meepodeep/meepolab/Key testing/Body140.3mf

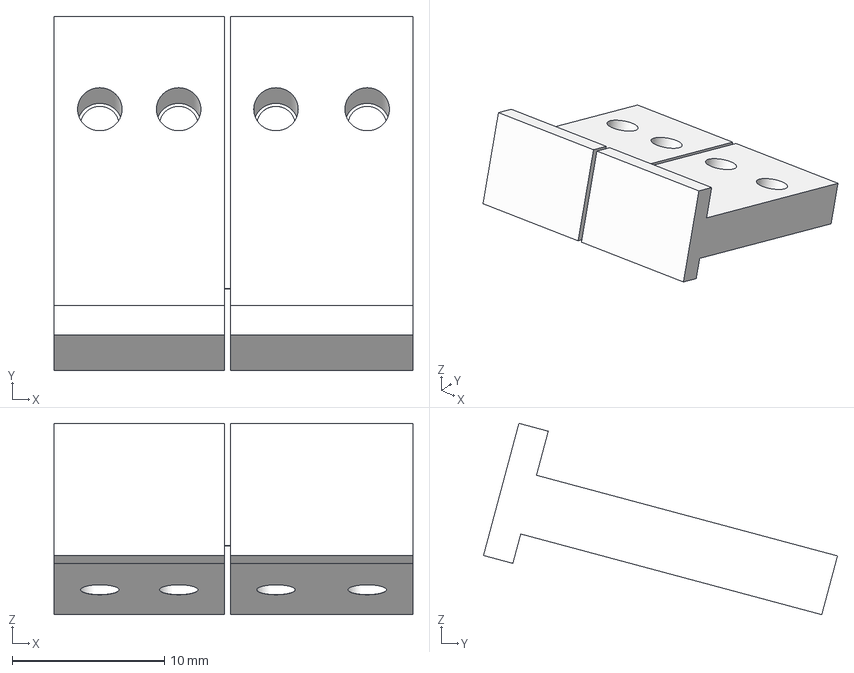
[picture p14: CAD file, 2026-06-28]
Key testing/Body140.3mf
23.6 x 23.3 x 12.6 mm
