meepodeep/meepolab/Key testing/BackPlate (2).3mf

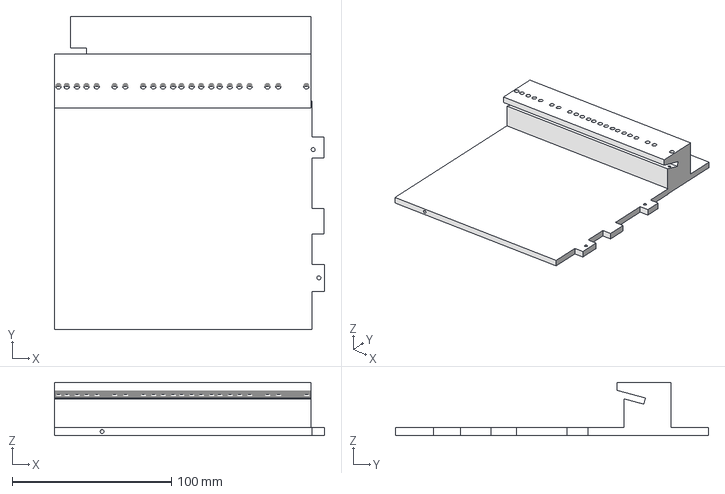
[picture p15: CAD file, 2026-06-28]
Key testing/BackPlate (2).3mf
169.5 x 196.6 x 33.3 mm
