meepodeep/meepolab/Key testing/Body30.3mf

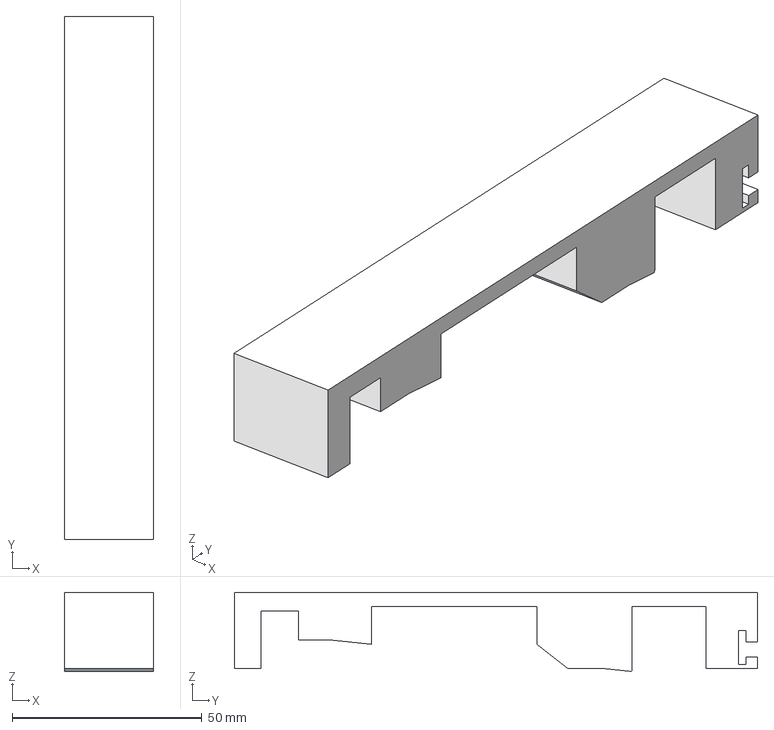
[picture p16: CAD file, 2026-06-28]
Key testing/Body30.3mf
23.6 x 138.0 x 20.8 mm
