meepodeep/meepolab/Cad Files/Case (2).3mf

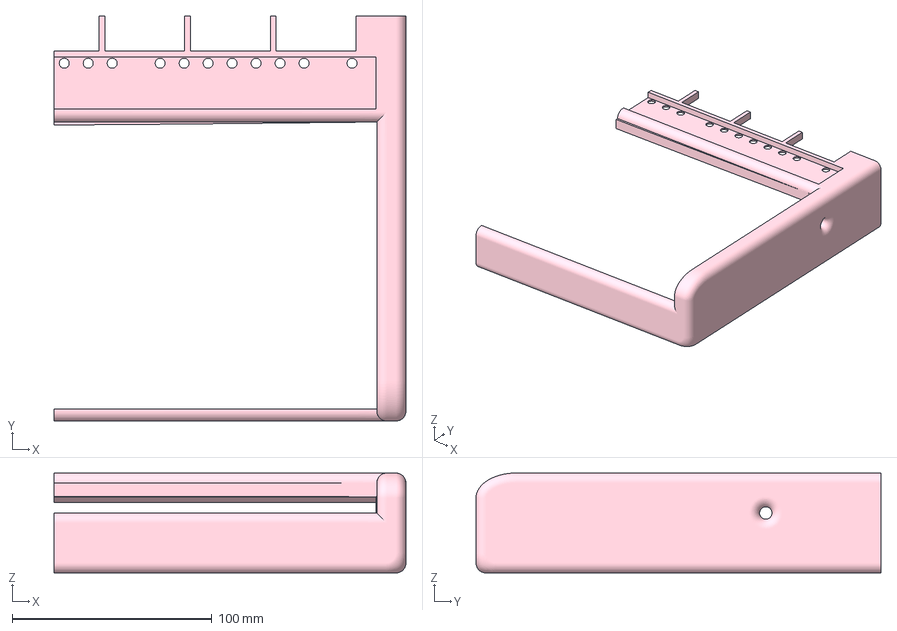
[picture p17: CAD file, 2026-06-28]
Cad Files/Case (2).3mf
176.1 x 202.6 x 50.0 mm
