meepodeep/meepolab/Key testing/Body161.3mf

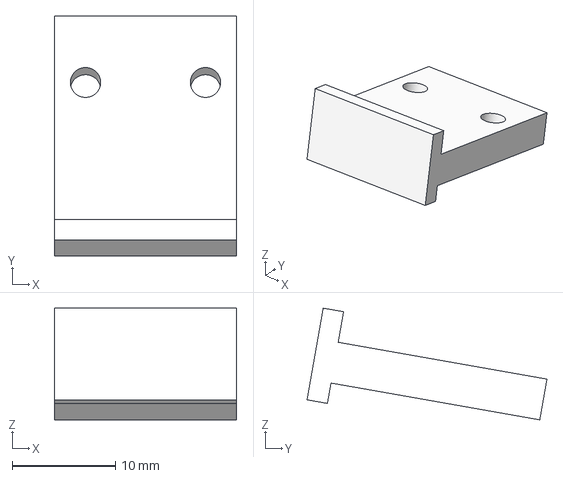
[picture p18: CAD file, 2026-06-28]
Key testing/Body161.3mf
17.6 x 23.2 x 10.8 mm
