meepodeep/meepolab/Key testing/tpu/Body215.3mf

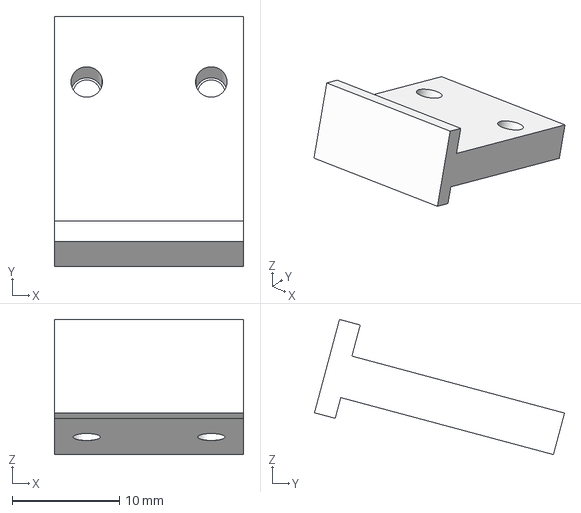
[picture p20: CAD file, 2026-06-28]
Key testing/tpu/Body215.3mf
17.6 x 23.3 x 12.6 mm
