meepodeep/meepolab/Cad Files/test spacer.3mf

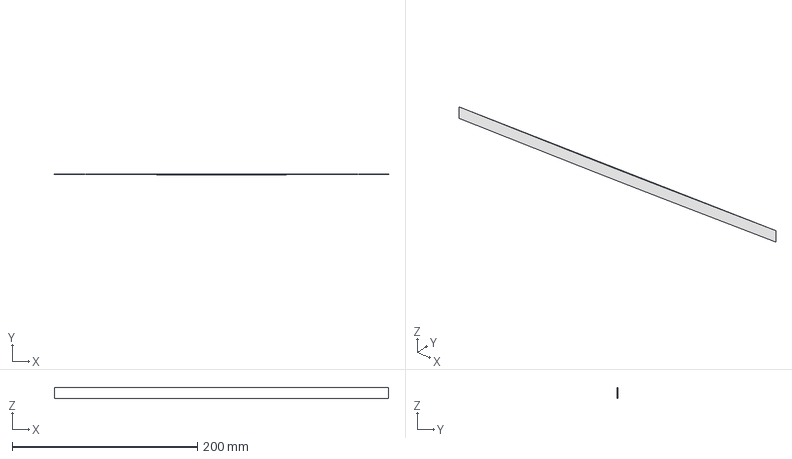
[picture p21: CAD file, 2026-06-28]
Cad Files/test spacer.3mf
360.8 x 1.05 x 11.9 mm
