meepodeep/meepolab/Cad Files/Key (18).3mf

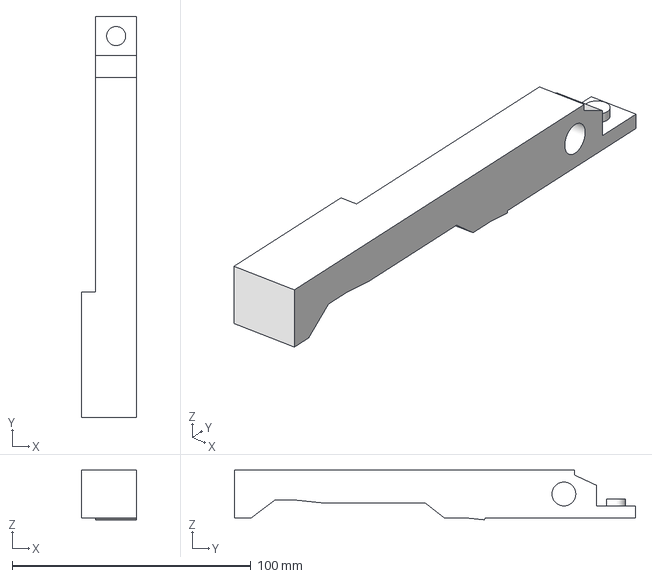
[picture p22: CAD file, 2026-06-28]
Cad Files/Key (18).3mf
23.2 x 168.0 x 20.8 mm
