meepodeep/meepolab/Key testing/backplatebottomleft.3mf

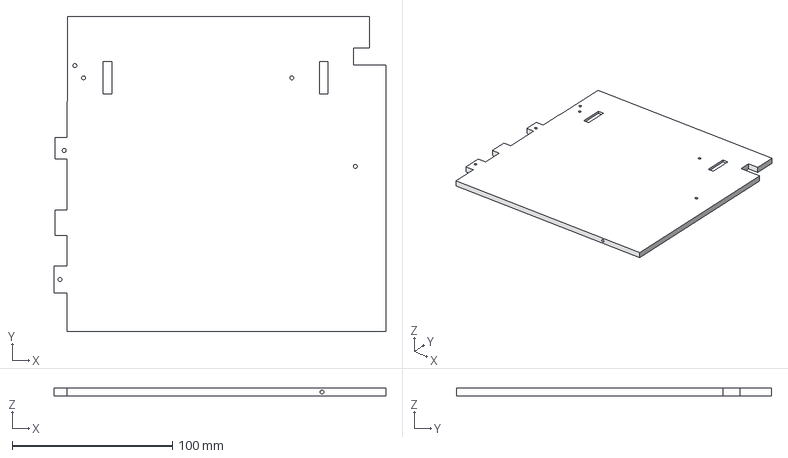
[picture p23: CAD file, 2026-06-28]
Key testing/backplatebottomleft.3mf
207.2 x 196.6 x 5.00 mm
