meepodeep/meepolab/Cad Files/rod test.3mf

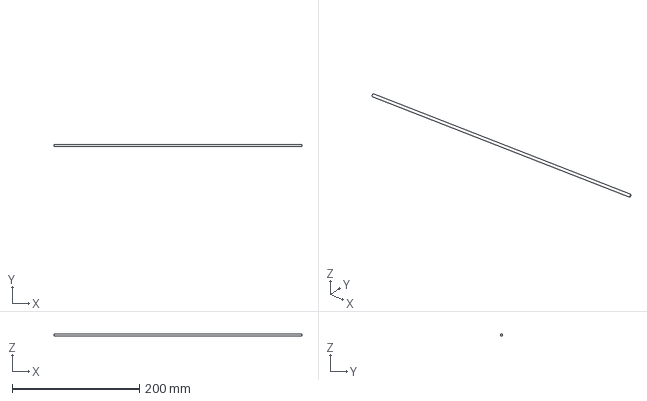
[picture p24: CAD file, 2026-06-28]
Cad Files/rod test.3mf
390.0 x 3.80 x 3.80 mm
