meepodeep/meepolab/Cad Files/Key (24).3mf

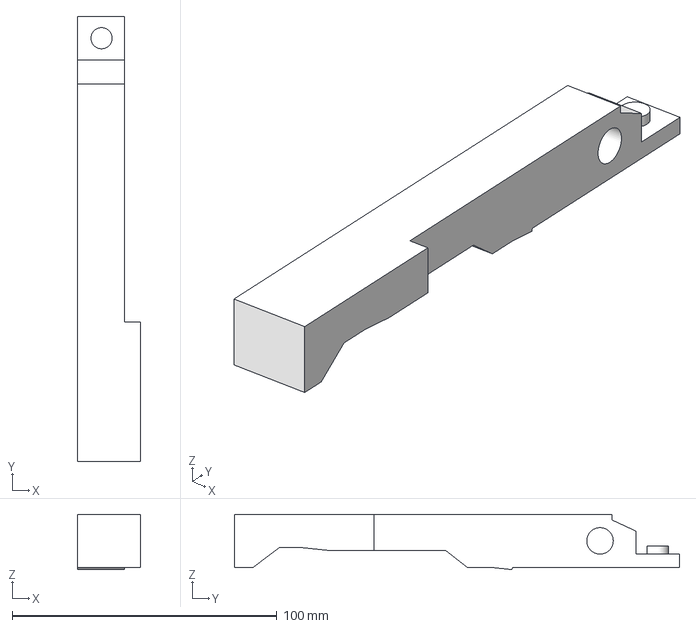
[picture p25: CAD file, 2026-06-28]
Cad Files/Key (24).3mf
23.6 x 168.0 x 20.8 mm
