meepodeep/meepolab/Key testing/backplatebottomright.3mf

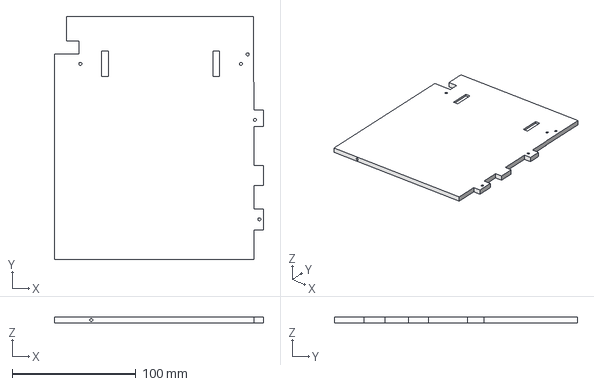
[picture p26: CAD file, 2026-06-28]
Key testing/backplatebottomright.3mf
169.5 x 196.6 x 5.00 mm
