meepodeep/meepolab/Key testing/tpu/Body207.3mf

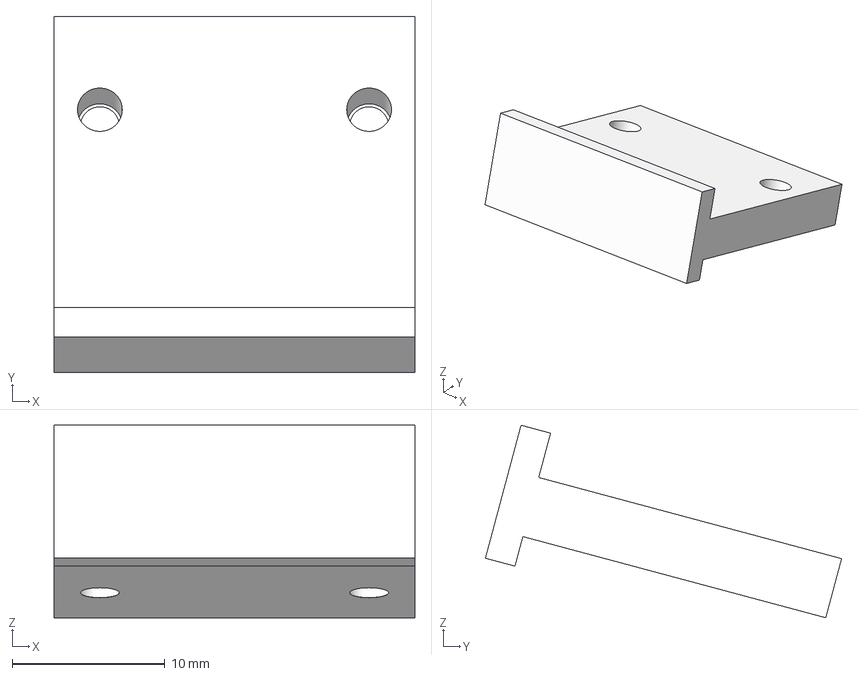
[picture p27: CAD file, 2026-06-28]
Key testing/tpu/Body207.3mf
23.6 x 23.3 x 12.6 mm
