meepodeep/meepolab/Cad Files/keys.step

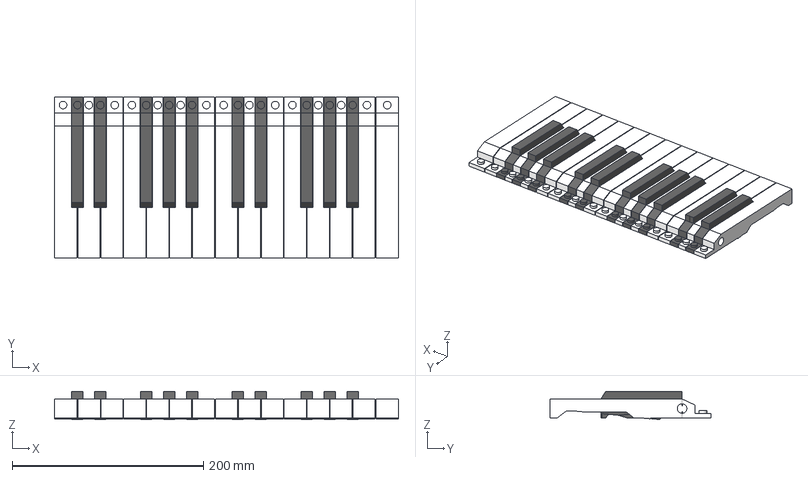
[picture p28: CAD file, 2026-06-28]
Cad Files/keys.step
360.0 x 168.0 x 29.6 mm
