meepodeep/meepolab/Cad Files/Keyplate.3mf

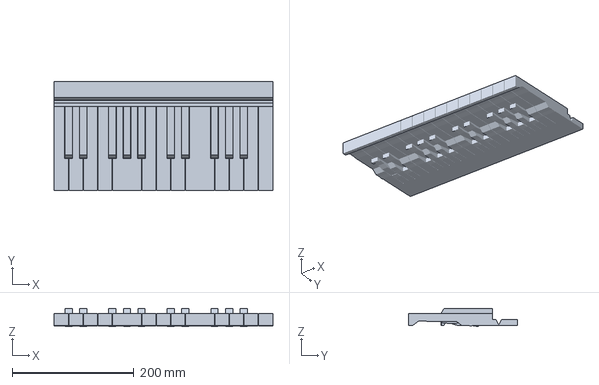
[picture p29: CAD file, 2026-06-28]
Cad Files/Keyplate.3mf
360.0 x 179.5 x 29.6 mm
