meepodeep/meepolab/Cad Files/Meepolab v12_Meepolab v12_pot accent.stl

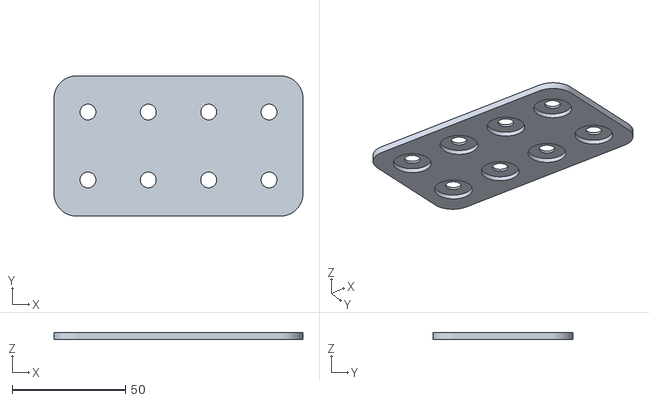
[picture p30: CAD file, 2026-06-28]
Cad Files/Meepolab v12_Meepolab v12_pot accent.stl
110.0 x 62.0 x 3.00
