meepodeep/meepolab/Key testing/Keymount.3mf

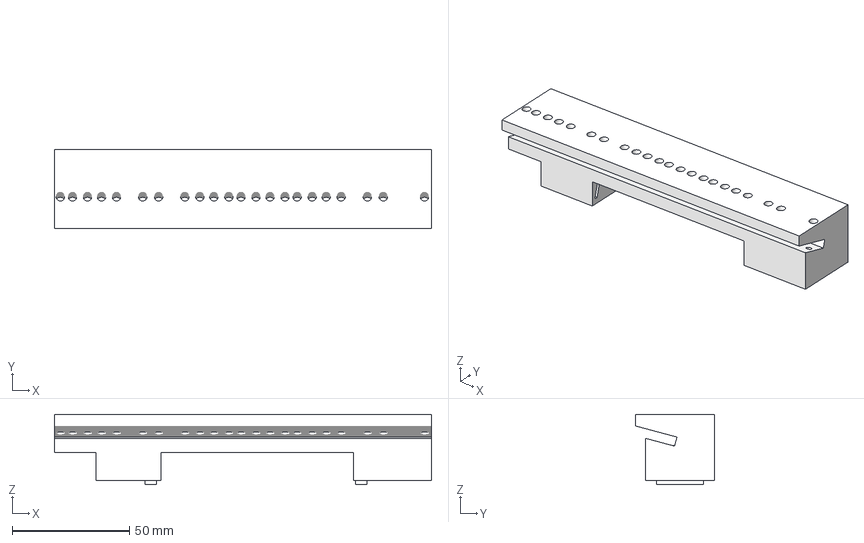
[picture p31: CAD file, 2026-06-28]
Key testing/Keymount.3mf
161.1 x 33.9 x 30.1 mm
