meepodeep/meepolab/Cad Files/Key.3mf

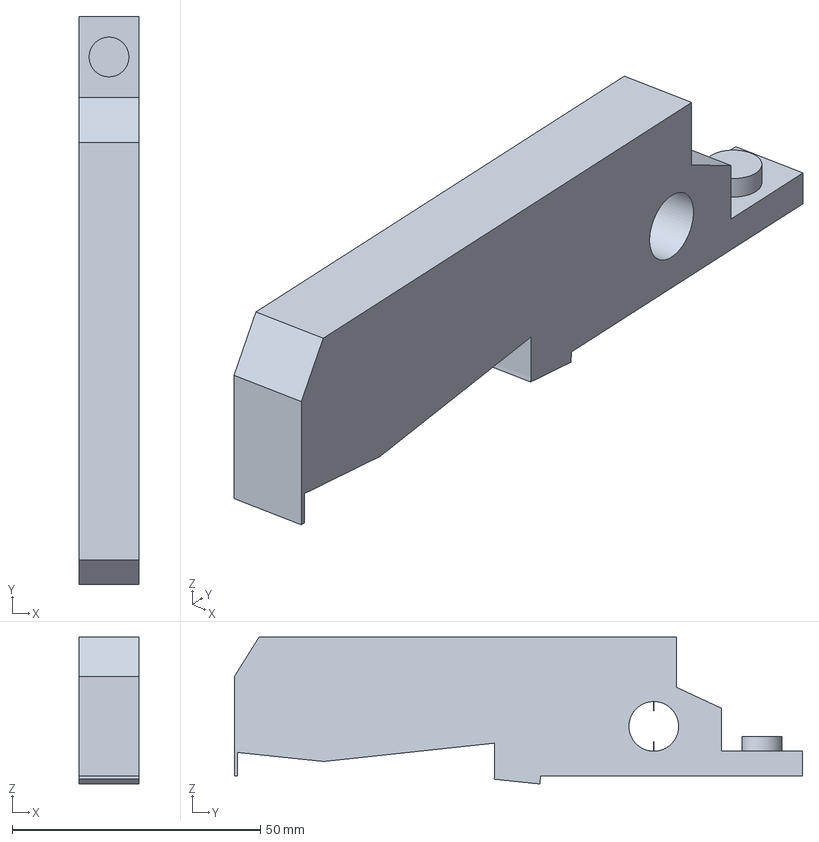
[picture p32: CAD file, 2026-06-28]
Cad Files/Key.3mf
12.0 x 114.5 x 29.6 mm
