meepodeep/meepolab/Cad Files/Key reinforcement.3mf

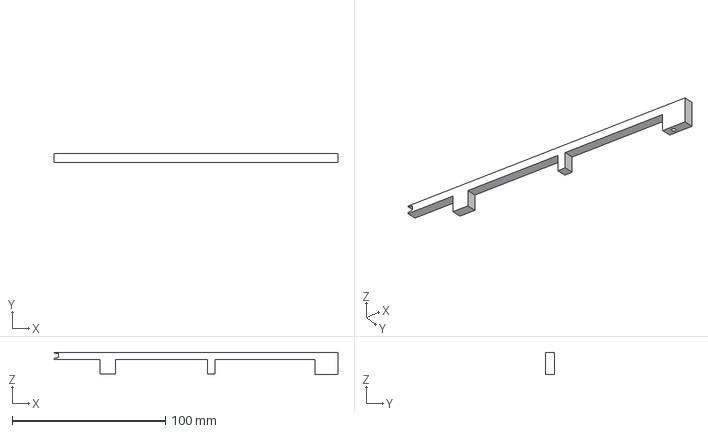
[picture p33: CAD file, 2026-06-28]
Cad Files/Key reinforcement.3mf
185.5 x 6.00 x 14.6 mm
