meepodeep/meepolab/Cad Files/Key (23).3mf

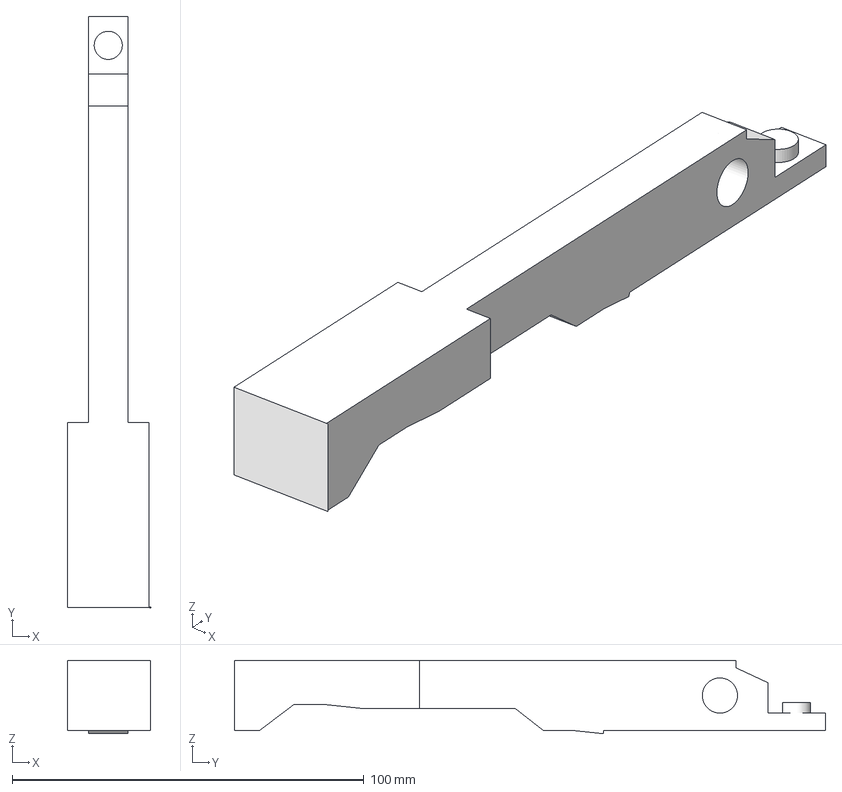
[picture p34: CAD file, 2026-06-28]
Cad Files/Key (23).3mf
23.6 x 168.0 x 20.8 mm
