meepodeep/meepolab/Cad Files/TactMount.3mf

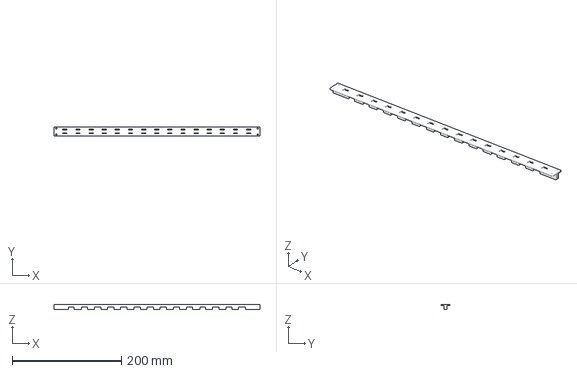
[picture p35: CAD file, 2026-06-28]
Cad Files/TactMount.3mf
376.8 x 17.0 x 9.80 mm
