meepodeep/meepolab/Cad Files/Meepolab v12_Meepolab v12_Case.stl

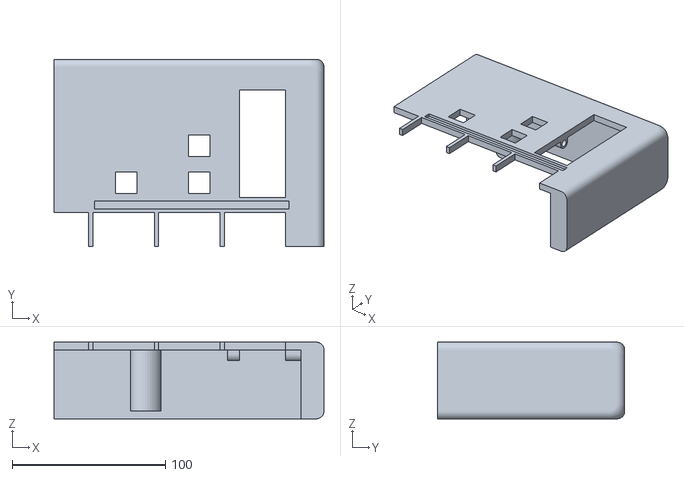
[picture p36: CAD file, 2026-04-06]
Cad Files/Meepolab v12_Meepolab v12_Case.stl
176.1 x 122.3 x 50.0
