meepodeep/meepolab/Cad Files/Meepolab v12_Meepolab v12_rocker switch mount.stl

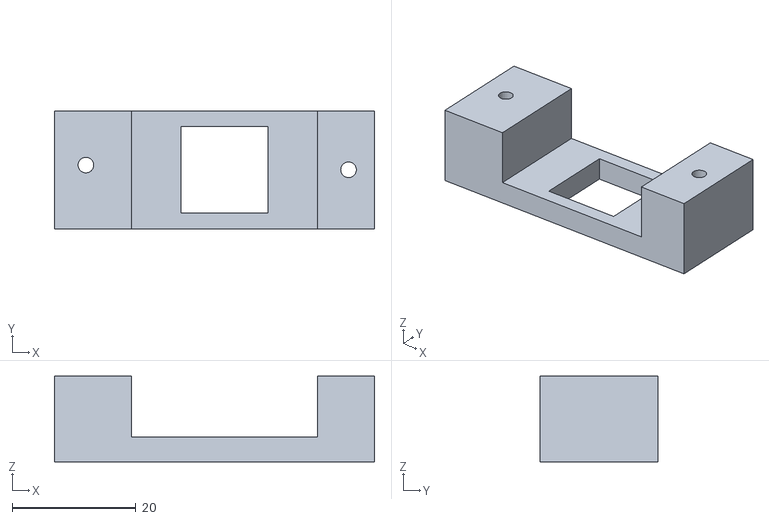
[picture p37: CAD file, 2026-04-06]
Cad Files/Meepolab v12_Meepolab v12_rocker switch mount.stl
51.6 x 19.1 x 13.8
