meepodeep/meepolab/Cad Files/Meepolab v12_Meepolab v12_Key (24).stl

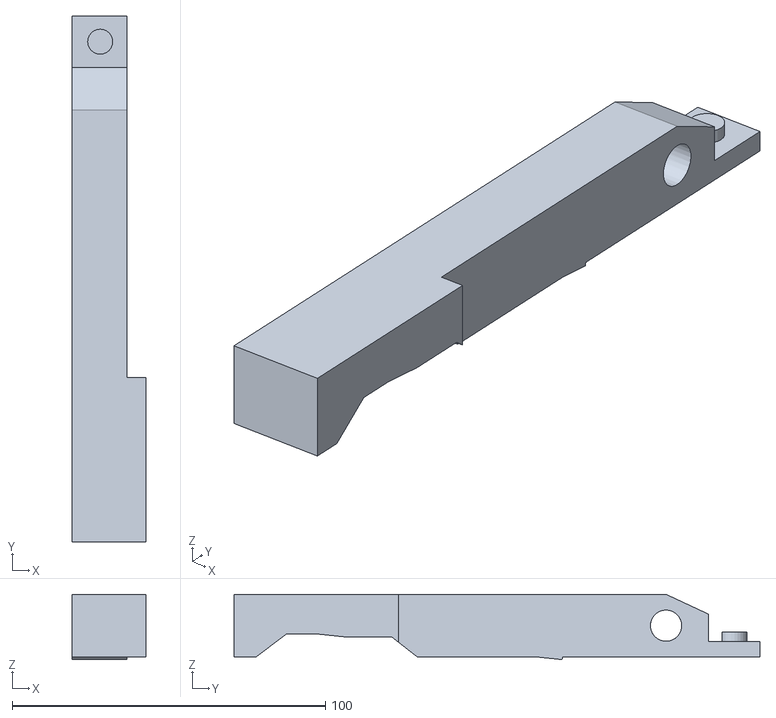
[picture p38: CAD file, 2026-04-06]
Cad Files/Meepolab v12_Meepolab v12_Key (24).stl
23.6 x 168.0 x 20.8
