meepodeep/meepolab/Cad Files/Meepolab v12_Meepolab v12_Component1_2_Body1.stl

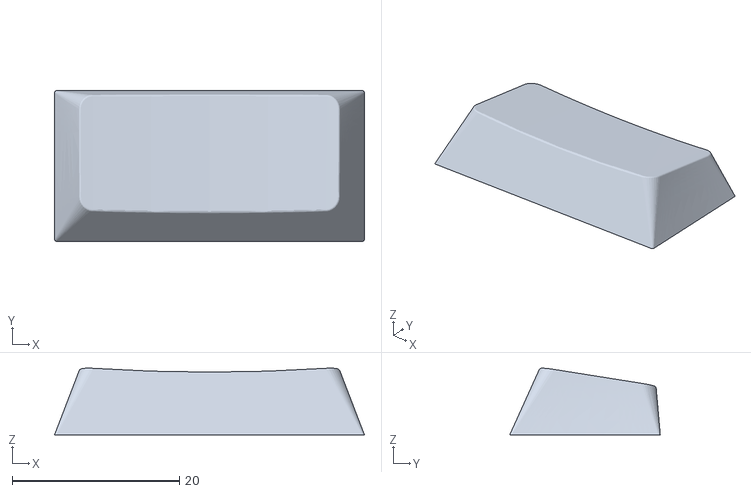
[picture p39: CAD file, 2026-04-06]
Cad Files/Meepolab v12_Meepolab v12_Component1_2_Body1.stl
37.0 x 18.0 x 7.98
