meepodeep/meepolab/Cad Files/Meepolab v12_Meepolab v12_Acrylic.stl

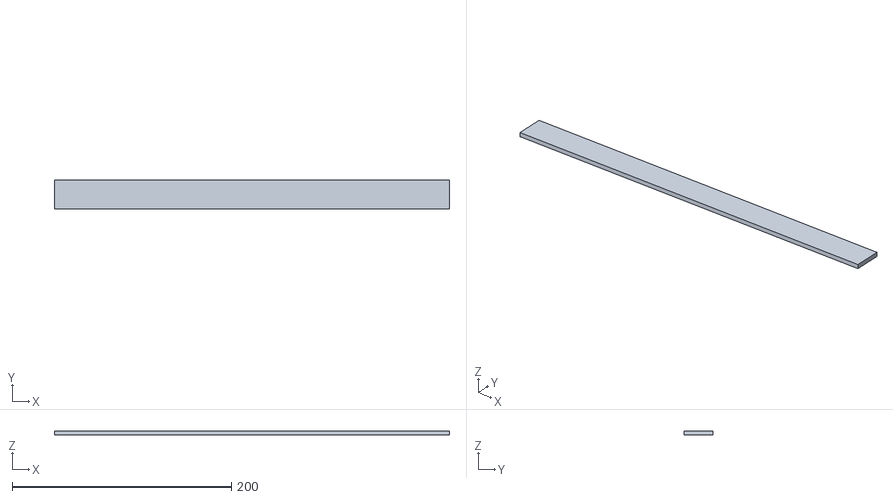
[picture p40: CAD file, 2026-04-06]
Cad Files/Meepolab v12_Meepolab v12_Acrylic.stl
360.0 x 26.0 x 4.00
