meepodeep/meepolab/Cad Files/Meepolab v12_Meepolab v12_KeyAxel.stl

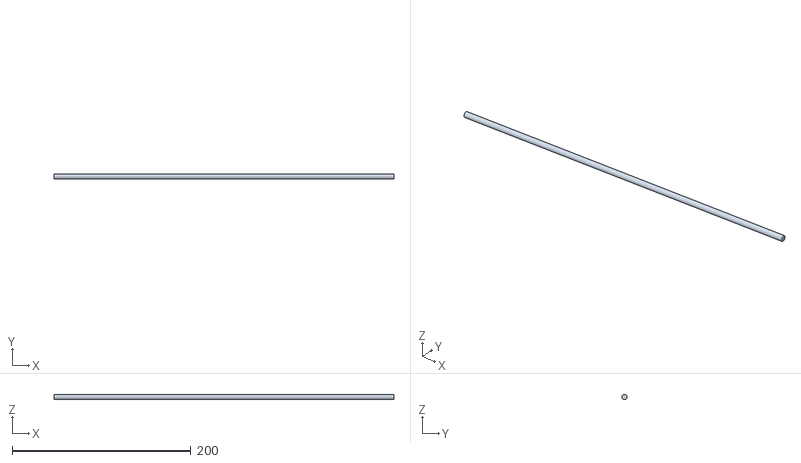
[picture p41: CAD file, 2026-04-06]
Cad Files/Meepolab v12_Meepolab v12_KeyAxel.stl
380.0 x 6.00 x 6.00
