meepodeep/meepolab/Cad Files/Meepolab v12_Meepolab v12_Key (20).stl

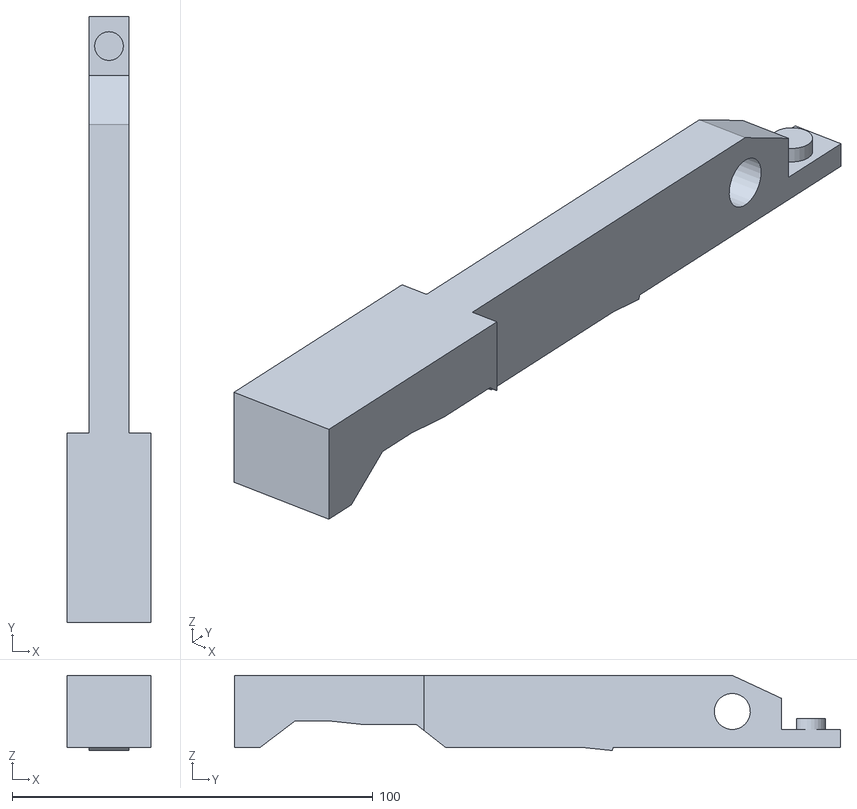
[picture p42: CAD file, 2026-04-06]
Cad Files/Meepolab v12_Meepolab v12_Key (20).stl
23.2 x 168.0 x 20.8
