meepodeep/meepolab/Cad Files/Meepolab v12_Meepolab v12_potentiometer cap.stl

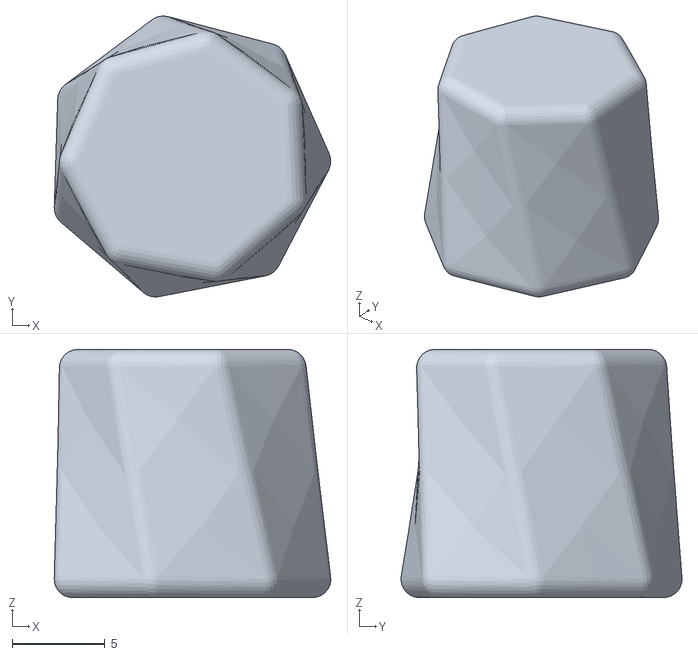
[picture p44: CAD file, 2026-04-06]
Cad Files/Meepolab v12_Meepolab v12_potentiometer cap.stl
14.9 x 15.2 x 13.4
