meepodeep/meepolab/Cad Files/Meepolab v12_Meepolab v12_Rocker.stl

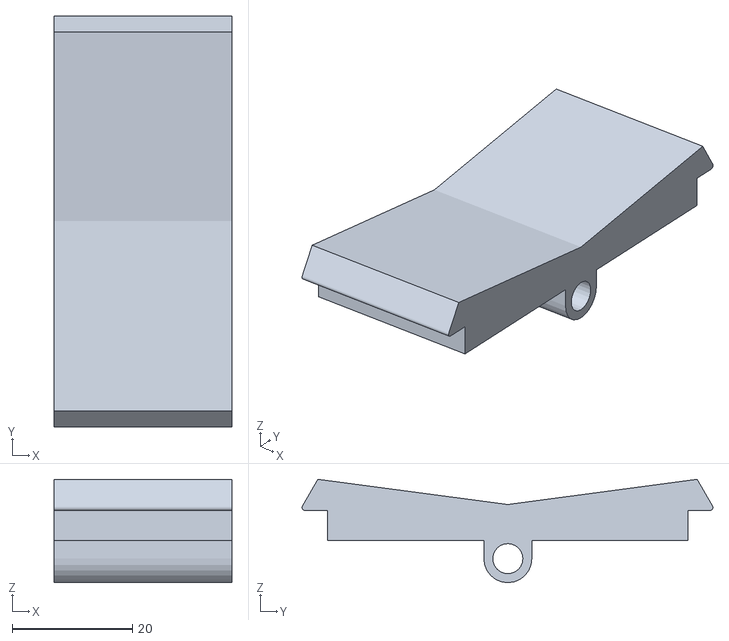
[picture p45: CAD file, 2026-04-06]
Cad Files/Meepolab v12_Meepolab v12_Rocker.stl
29.6 x 68.4 x 17.2
