meepodeep/meepolab/Cad Files/Meepolab v12_Meepolab v12_Slider.stl

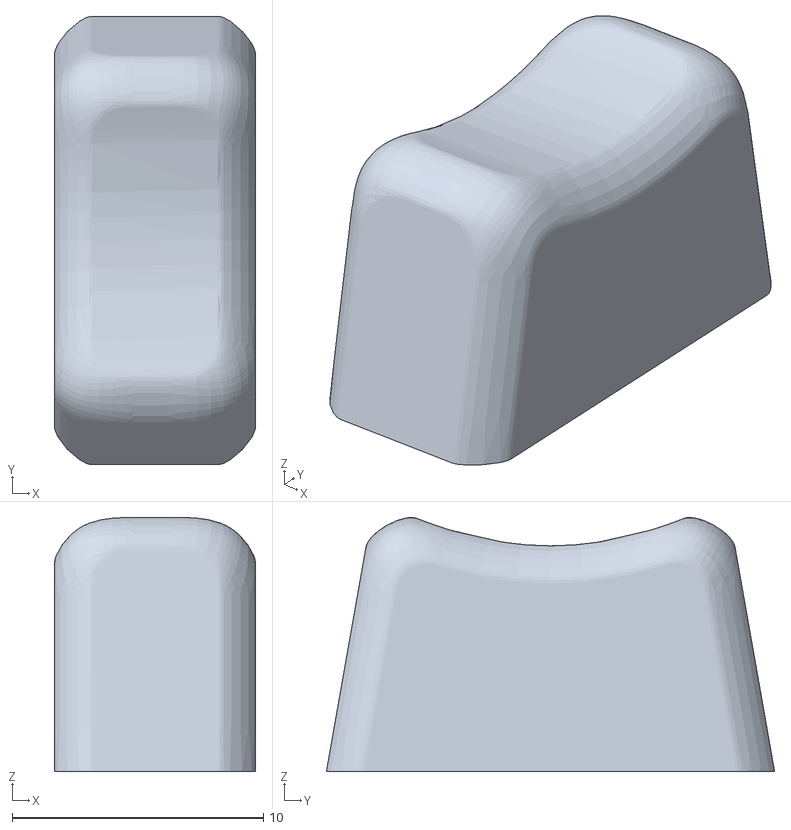
[picture p46: CAD file, 2026-04-06]
Cad Files/Meepolab v12_Meepolab v12_Slider.stl
8.00 x 17.8 x 10.1
