meepodeep/meepolab/Cad Files/Meepolab v12_Meepolab v12_Rocker Axel.stl

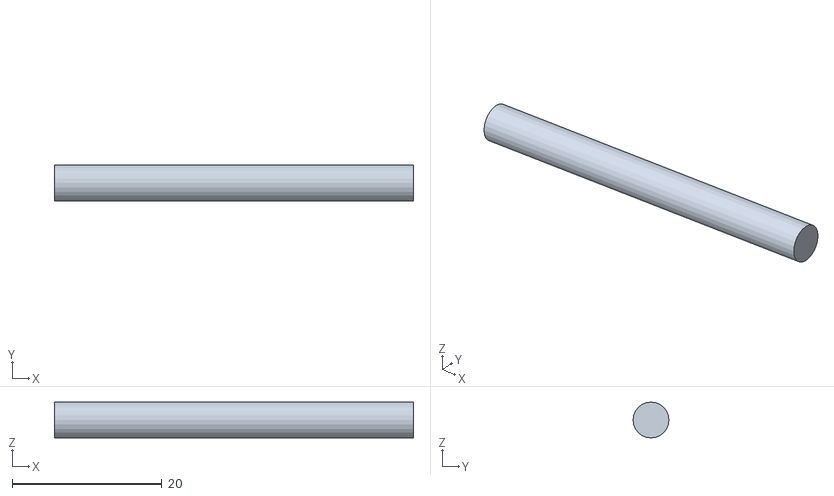
[picture p47: CAD file, 2026-04-06]
Cad Files/Meepolab v12_Meepolab v12_Rocker Axel.stl
48.0 x 4.80 x 4.80
