meepodeep/meepolab/Cad Files/Meepolab v12_Meepolab v12_Slider Accent.stl

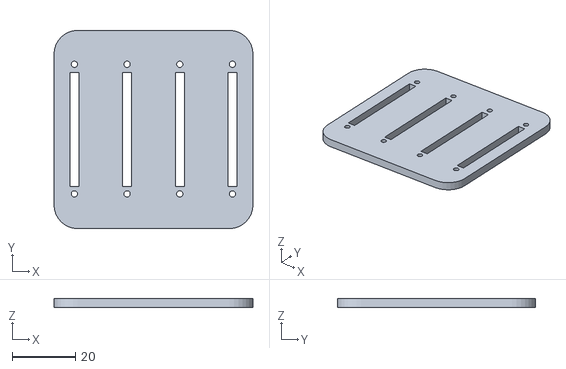
[picture p48: CAD file, 2026-04-06]
Cad Files/Meepolab v12_Meepolab v12_Slider Accent.stl
63.0 x 62.7 x 3.00
