meepodeep/meepolab/Cad Files/Meepolab v12_Meepolab v12_Key.stl

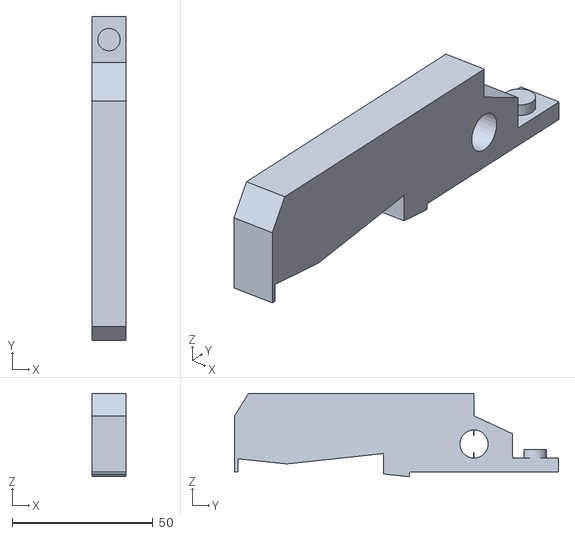
[picture p49: CAD file, 2026-04-06]
Cad Files/Meepolab v12_Meepolab v12_Key.stl
12.0 x 115.0 x 29.6
