meepodeep/meepolab/Cad Files/Meepolab v12_Meepolab v12_Body82.stl

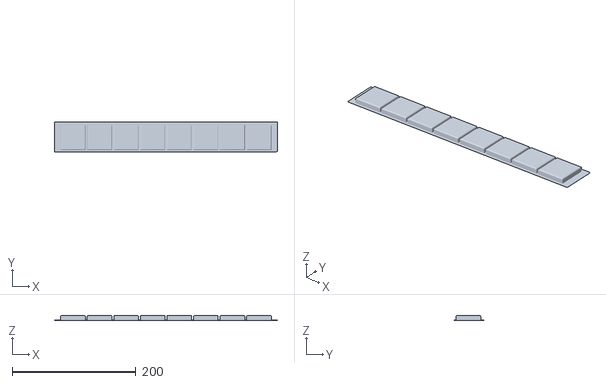
[picture p50: CAD file, 2026-04-06]
Cad Files/Meepolab v12_Meepolab v12_Body82.stl
360.0 x 48.0 x 8.00
