meepodeep/meepolab/Cad Files/Meepolab v12_Meepolab v12_Case Accent.stl

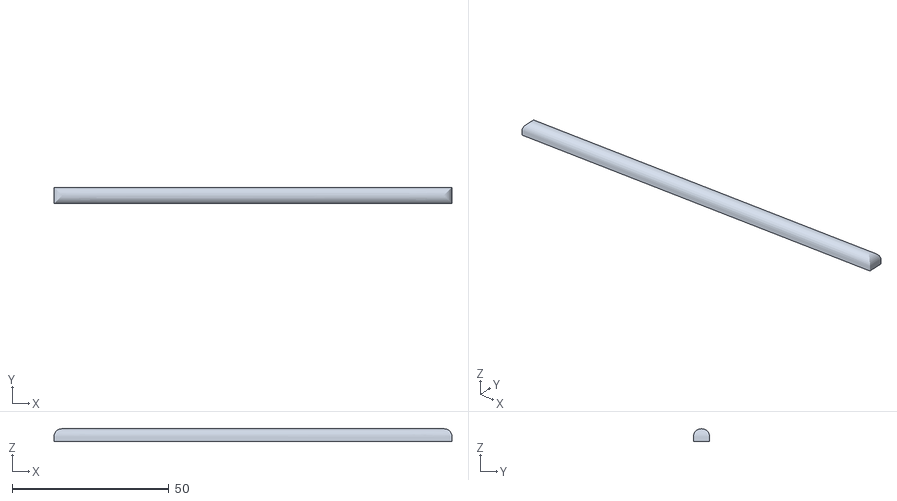
[picture p51: CAD file, 2026-04-06]
Cad Files/Meepolab v12_Meepolab v12_Case Accent.stl
127.0 x 5.16 x 4.00
