meepodeep/meepolab/Cad Files/Meepolab v12_Meepolab v12_Key (12).stl

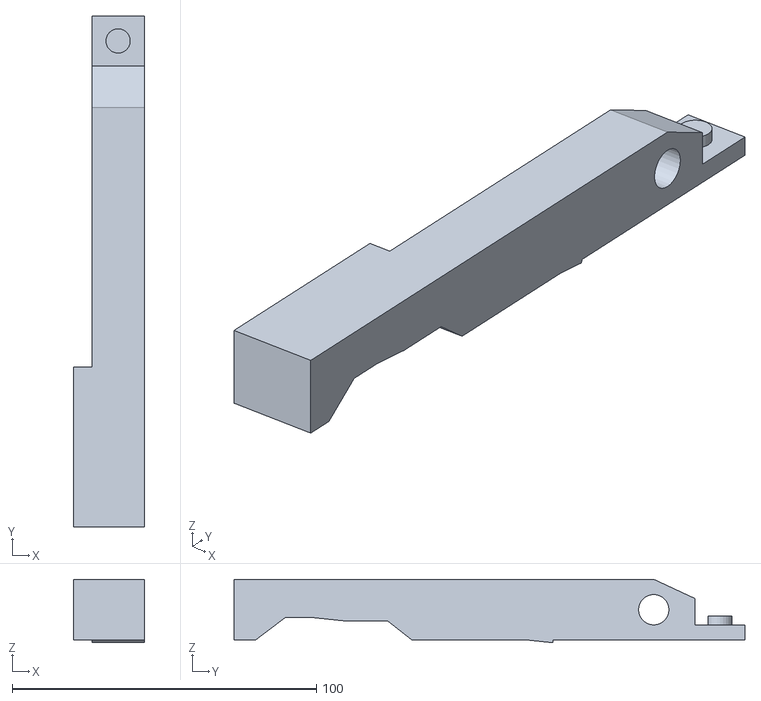
[picture p52: CAD file, 2026-04-06]
Cad Files/Meepolab v12_Meepolab v12_Key (12).stl
23.2 x 168.0 x 20.8
